tkodev/frm-proton/assets/cover.jpg

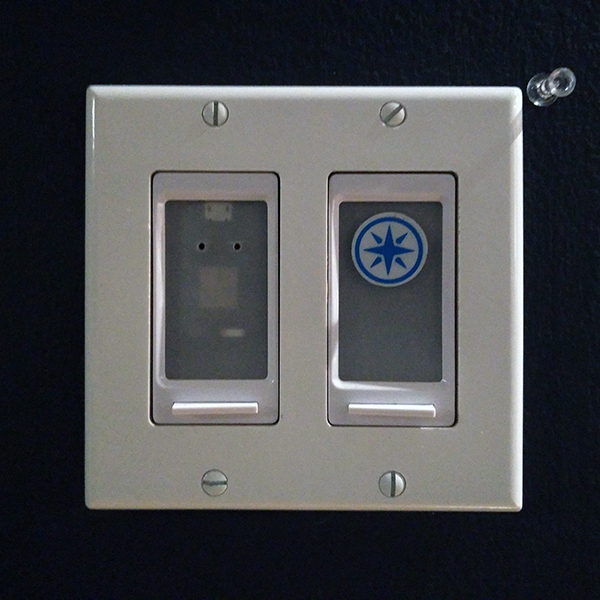
assets/cover.jpg
